Nils2332/Big-Stopwatch/Hardware/Counter/CAD-files/BatCap.stl

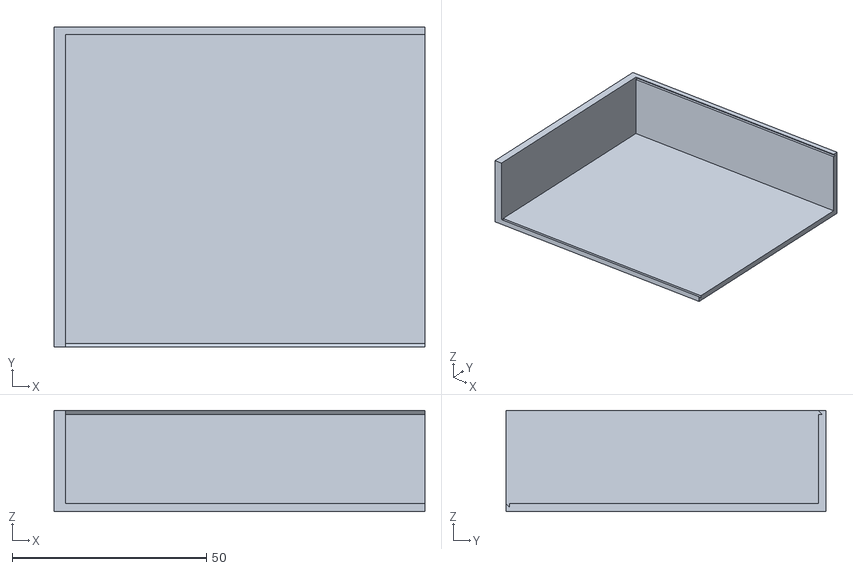
[picture p20: CAD file, 2019-07-28]
Hardware/Counter/CAD-files/BatCap.stl
95.5 x 82.5 x 26.0
