Nils2332/Big-Stopwatch/Hardware/Counter/CAD-files/Batcap2.stl

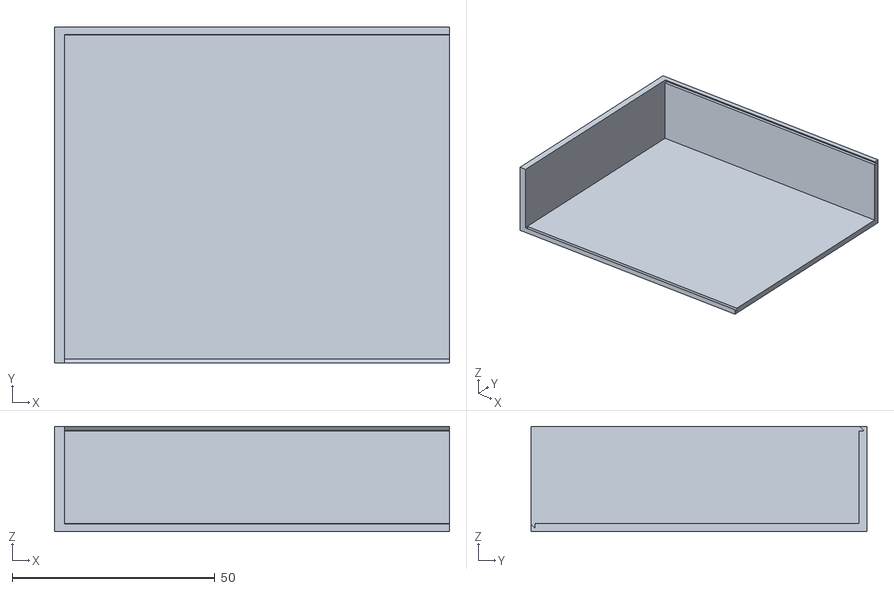
[picture p21: CAD file, 2019-07-28]
Hardware/Counter/CAD-files/Batcap2.stl
97.5 x 83.0 x 26.0
