Nils2332/Big-Stopwatch/Hardware/Counter/CAD-files/Bauteil3.stl

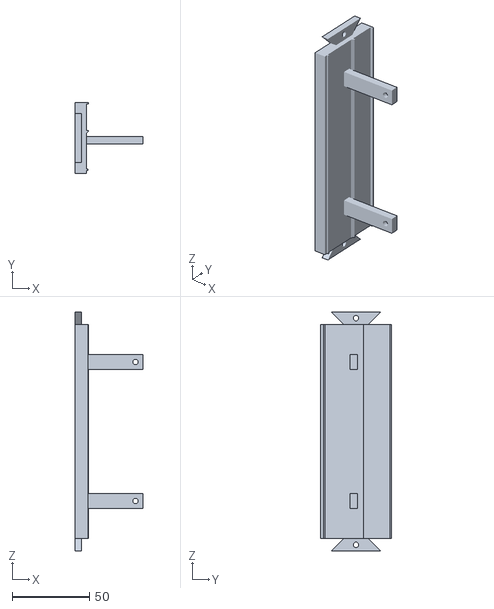
[picture p22: CAD file, 2019-07-28]
Hardware/Counter/CAD-files/Bauteil3.stl
44.2 x 46.0 x 154.8
