Nils2332/Big-Stopwatch/Hardware/Counter/CAD-files/Cover-7-Segment.stl

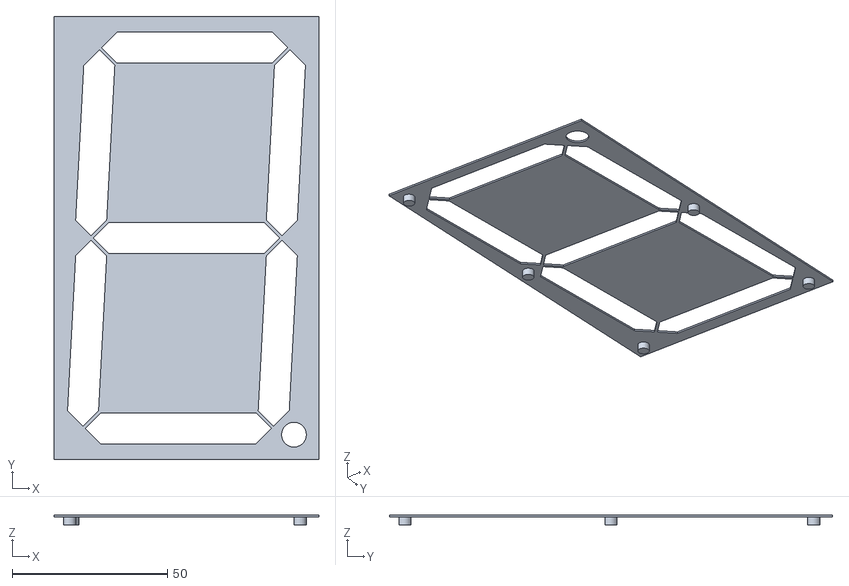
[picture p23: CAD file, 2019-07-28]
Hardware/Counter/CAD-files/Cover-7-Segment.stl
85.2 x 142.7 x 3.10
