Nils2332/Big-Stopwatch/Hardware/Counter/CAD-files/Backplate.stl

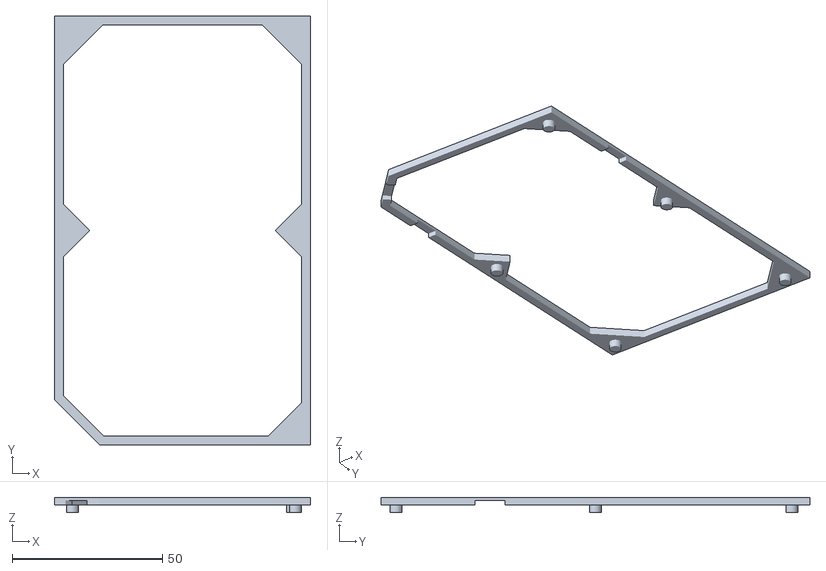
[picture p24: CAD file, 2019-07-28]
Hardware/Counter/CAD-files/Backplate.stl
85.2 x 142.7 x 5.00
