Nils2332/Big-Stopwatch/Hardware/Counter/CAD-files/Segment_V4.stl

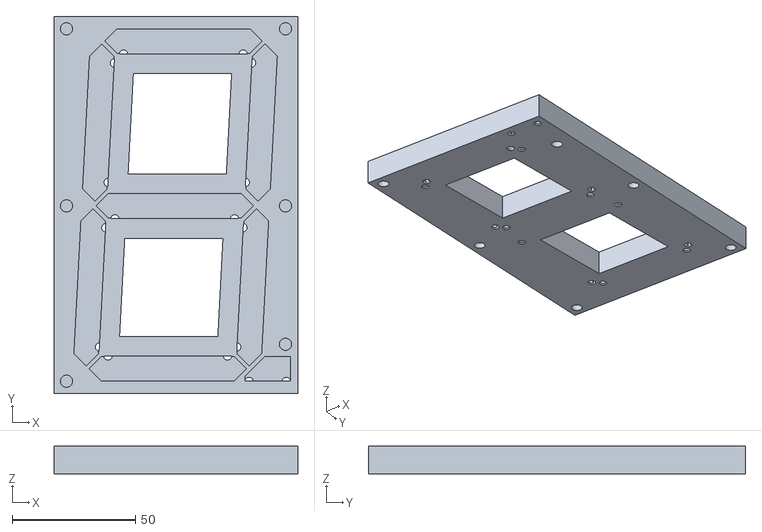
[picture p25: CAD file, 2019-07-28]
Hardware/Counter/CAD-files/Segment_V4.stl
99.0 x 153.2 x 11.3
