Nils2332/Big-Stopwatch/Hardware/Counter/CAD-files/Case-Side.stl

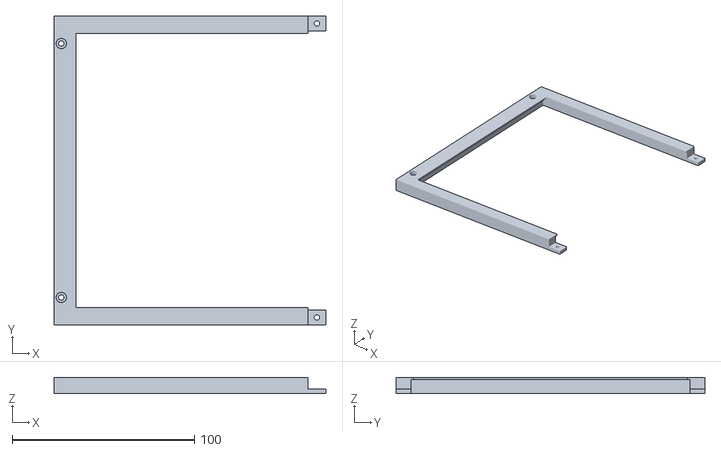
[picture p26: CAD file, 2019-07-28]
Hardware/Counter/CAD-files/Case-Side.stl
149.4 x 169.5 x 8.90
