Nils2332/Big-Stopwatch/Hardware/Counter/CAD-files/Knopf.stl

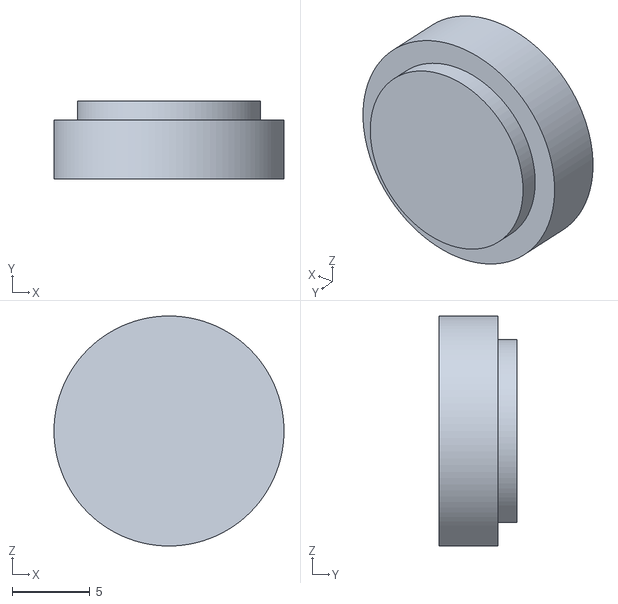
[picture p27: CAD file, 2019-07-28]
Hardware/Counter/CAD-files/Knopf.stl
14.8 x 5.00 x 14.8
