Nils2332/Big-Stopwatch/Hardware/Counter/CAD-files/Backplate-housing.stl

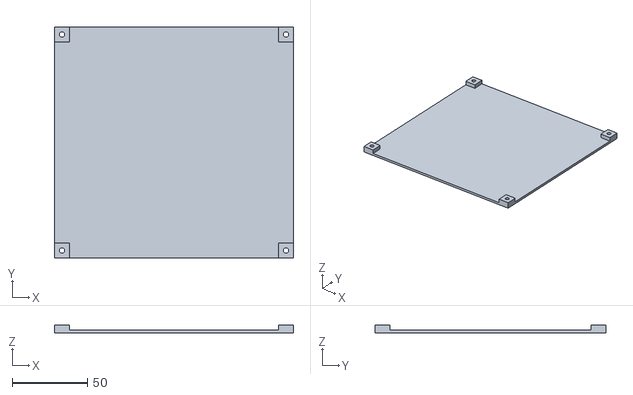
[picture p28: CAD file, 2019-07-28]
Hardware/Counter/CAD-files/Backplate-housing.stl
158.8 x 153.5 x 5.50
