Nils2332/Big-Stopwatch/Hardware/Counter/CAD-files/Backplate_V2.stl

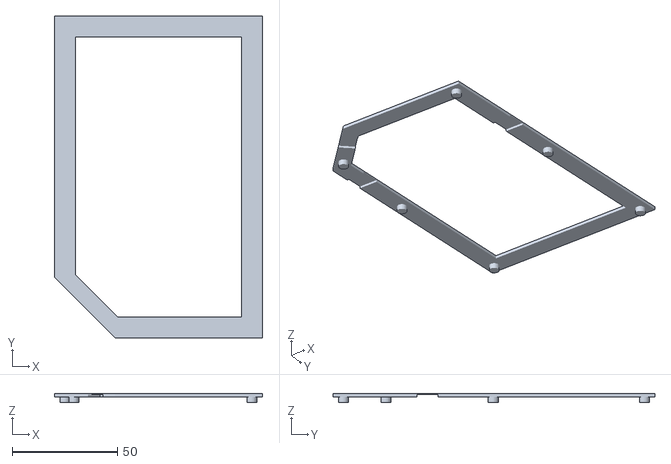
[picture p29: CAD file, 2019-07-28]
Hardware/Counter/CAD-files/Backplate_V2.stl
99.0 x 153.2 x 4.10
