Nils2332/Big-Stopwatch/Hardware/Counter/CAD-files/Case_side_back_MIR.stl

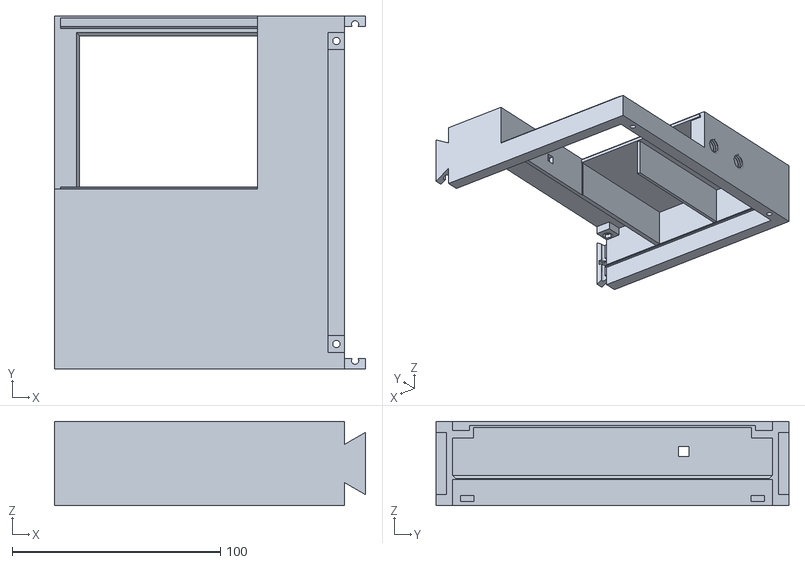
[picture p30: CAD file, 2019-07-28]
Hardware/Counter/CAD-files/Case_side_back_MIR.stl
149.4 x 169.5 x 40.5
