Nils2332/Big-Stopwatch/Hardware/Counter/CAD-files/Case_top_back.stl

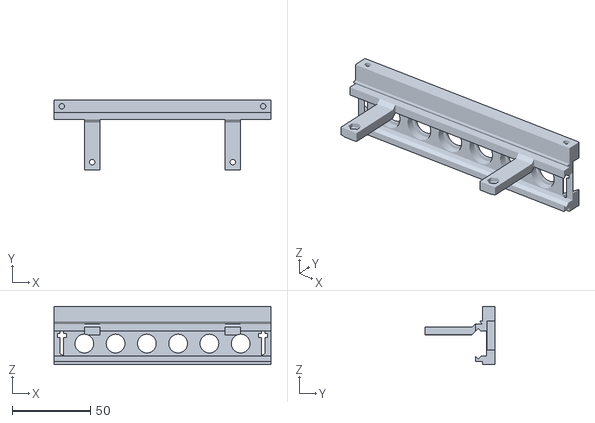
[picture p31: CAD file, 2019-07-28]
Hardware/Counter/CAD-files/Case_top_back.stl
138.8 x 44.8 x 37.3
