Nils2332/Big-Stopwatch/Hardware/Counter/CAD-files/Segment.stl

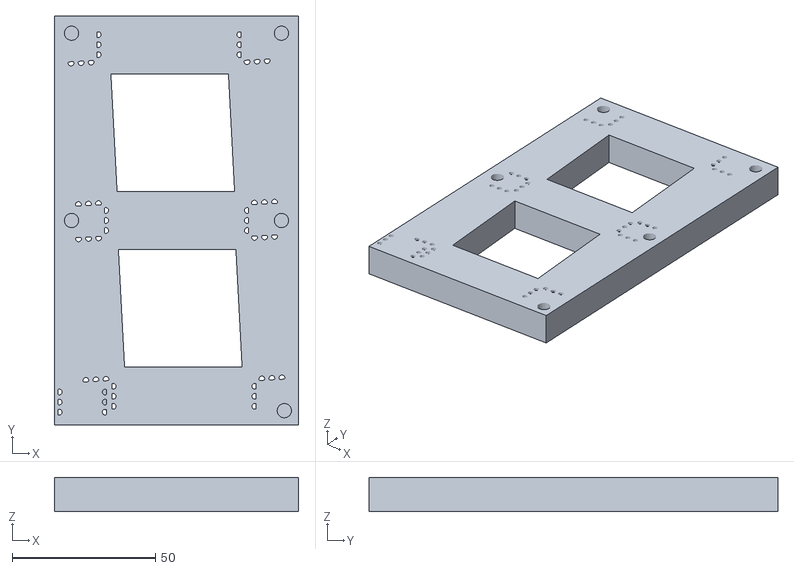
[picture p32: CAD file, 2019-07-28]
Hardware/Counter/CAD-files/Segment.stl
85.2 x 142.7 x 12.0
