Nils2332/Big-Stopwatch/Software/Counter/7SegmentTimer06.ino/Debug.h

//Nils Schröder
//03.10.2018

#include "LCD.h"

#pragma once
#ifndef Debug_H
#define Debug_H

void anidigitdemo(LEDLCD LCD);

void showdemo(LEDLCD LCD);

void anishowdemo(LEDLCD LCD);

#endif // Debug_H
